frankjoshua/rfid_lock/rfid_lock_sketch/lock.ino

#define LOCK_PIN D8
#define LOCK_INPUT 10

#define LOCK_ENGAGE_STATE HIGH

void initLock(){
  pinMode(LOCK_PIN, OUTPUT);
  pinMode(LOCK_INPUT, INPUT);
  lock();
}

void unlock(){
  digitalWrite(LOCK_PIN, LOCK_ENGAGE_STATE);
}

void lock(){
  digitalWrite(LOCK_PIN, !LOCK_ENGAGE_STATE);
}

boolean isLockEngaged(){
  return digitalRead(LOCK_INPUT) == LOCK_ENGAGE_STATE;
}
