frankjoshua/rfid_lock/rfid_lock_sketch/icons.h

/**
 * Convert icons to byte array with this site
 * http://makertum.com/en/bytearray-maker/
 * Using open source icons from
 * https://material.io/resources/icons  (Make sure to use white ones)
 */

#ifndef icons_h
#define icons_h

uint16_t LOCK_BMP_W=20;
uint16_t LOCK_BMP_H=20;
static const unsigned char PROGMEM LOCK_BMP[] = {
  B00000001, B11100000, B0000,
  B00000011, B11110000, B0000,
  B00000111, B11111000, B0000,
  B00000111, B00111000, B0000,
  B00000110, B00011000, B0000,
  B00000000, B00011000, B0000,
  B00011111, B11111110, B0000,
  B00011111, B11111110, B0000,
  B00011000, B00000110, B0000,
  B00011000, B11000110, B0000,
  B00011001, B11100110, B0000,
  B00011001, B11100110, B0000,
  B00011001, B11100110, B0000,
  B00011000, B00000110, B0000,
  B00011000, B00000110, B0000,
  B00011111, B11111110, B0000,
  B00011111, B11111110, B0000,
  B00000000, B00000000, B0000,
  B00000000, B00000000, B0000,
  B00000000, B00000000, B0000
};

uint16_t UNLOCK_BMP_W=20;
uint16_t UNLOCK_BMP_H=20;
static const unsigned char PROGMEM UNLOCK_BMP[] = {
  B00000001, B11100000, B0000,
  B00000011, B11110000, B0000,
  B00000111, B11111000, B0000,
  B00000111, B00111000, B0000,
  B00000110, B00011000, B0000,
  B00000110, B00011000, B0000,
  B00011111, B11111110, B0000,
  B00011111, B11111110, B0000,
  B00011111, B11111110, B0000,
  B00011111, B11111110, B0000,
  B00011111, B11111110, B0000,
  B00011111, B00111110, B0000,
  B00011111, B11111110, B0000,
  B00011111, B11111110, B0000,
  B00011111, B11111110, B0000,
  B00011111, B11111110, B0000,
  B00011111, B11111110, B0000,
  B00000000, B00000000, B0000,
  B00000000, B00000000, B0000,
  B00000000, B00000000, B0000
};

uint16_t KEY_BMP_W=20;
uint16_t KEY_BMP_H=20;
static const unsigned char PROGMEM KEY_BMP[] = {
  B00000000, B00000000, B0000,
  B00000000, B00000000, B0000,
  B00000000, B00000000, B0000,
  B00000000, B00000000, B0000,
  B00011111, B00000000, B0000,
  B01111111, B10000000, B0000,
  B01111111, B11000000, B0000,
  B01111111, B11111111, B1100,
  B11111011, B11111111, B1100,
  B11111011, B11111111, B1100,
  B01111111, B11111111, B1100,
  B01111111, B11001111, B0000,
  B01111111, B10001111, B0000,
  B00011111, B00001111, B0000,
  B00000000, B00000000, B0000,
  B00000000, B00000000, B0000,
  B00000000, B00000000, B0000,
  B00000000, B00000000, B0000,
  B00000000, B00000000, B0000,
  B00000000, B00000000, B0000
};

#endif
